OldRadioGuy2/Arduino-Controlled-Radio/Software/Arduino/src/commands.h

/*
Software Controlled Radio - Command Definitions
*/

#ifndef COMMANDS_H
#define COMMANDS_H

#define triggerPin      13       // pin to charge the capacitor - connected to one end of the charging resistor
#define pulseInPin      10
#define digitalBandSwitch    A1

#define analogVolumePin      0
#define analogBandSwitch     1

#define BLE_TxPin      11 
#define BLE_RxPin      12

#define RSP_BUF_SIZE 40

typedef const char * processor_t(char * cmd);
typedef processor_t * processor_p;

typedef struct {
    char cmd[4];
    processor_p processor;
} command;

const char * read_Cap(char * cmd);
processor_t set_freq;
processor_t set_band;
processor_t set_volume;

processor_t get_sig_lvl;
processor_t get_freq;
processor_t get_band;
processor_t get_volume;

processor_t volume_feature;
processor_t tuning_feature;
processor_t band_sw_feature;
processor_t display_feature;
processor_t save_cfg;
processor_t create_band;
processor_t delete_band;
processor_t calibrate_tuner;
processor_t calibrate_band;

// extern command command_list[];
// Error codes (commands always return * strings)
// #define SUCCESS "0"
// #define INVALID_COMMAND "-1"
// #define INVALID_ARG "-2"

extern char dbg_verbose;
extern char fmt_rsp_buffer[RSP_BUF_SIZE];

#endif
