OldRadioGuy2/Arduino-Controlled-Radio/Software/PC/src/gui/MainWindow.py

# -*- coding: utf-8 -*-

###########################################################################
## Python code generated with wxFormBuilder (version Oct 26 2018)
## http://www.wxformbuilder.org/
##
## PLEASE DO *NOT* EDIT THIS FILE!
###########################################################################

import wx
import wx.xrc

###########################################################################
## Class MainWindow
###########################################################################

class MainWindow ( wx.Frame ):

	def __init__( self, parent ):
		wx.Frame.__init__ ( self, parent, id = wx.ID_ANY, title = u"Arduino Radio", pos = wx.DefaultPosition, size = wx.Size( 729,700 ), style = wx.DEFAULT_FRAME_STYLE|wx.TAB_TRAVERSAL )

		self.SetSizeHints( wx.DefaultSize, wx.DefaultSize )

		self.m_menubar1 = wx.MenuBar( 0 )
		self.m_menu1 = wx.Menu()
		self.file_select_port = wx.MenuItem( self.m_menu1, wx.ID_ANY, u"Select Serial Port", wx.EmptyString, wx.ITEM_NORMAL )
		self.m_menu1.Append( self.file_select_port )

		self.file_load_config = wx.MenuItem( self.m_menu1, wx.ID_ANY, u"Load Configuration", wx.EmptyString, wx.ITEM_NORMAL )
		self.m_menu1.Append( self.file_load_config )

		self.file_save_config = wx.MenuItem( self.m_menu1, wx.ID_ANY, u"Save Configuration", wx.EmptyString, wx.ITEM_NORMAL )
		self.m_menu1.Append( self.file_save_config )

		self.file_exit = wx.MenuItem( self.m_menu1, wx.ID_ANY, u"Exit", wx.EmptyString, wx.ITEM_NORMAL )
		self.m_menu1.Append( self.file_exit )

		self.m_menubar1.Append( self.m_menu1, u"File" )

		self.m_menu4 = wx.Menu()
		self.configure_configure = wx.MenuItem( self.m_menu4, wx.ID_ANY, u"Configure", wx.EmptyString, wx.ITEM_NORMAL )
		self.m_menu4.Append( self.configure_configure )

		self.m_menubar1.Append( self.m_menu4, u"Configure" )

		self.m_menu2 = wx.Menu()
		self.m_menubar1.Append( self.m_menu2, u"Calibrate" )

		self.m_menu3 = wx.Menu()
		self.m_menubar1.Append( self.m_menu3, u"Help" )

		self.SetMenuBar( self.m_menubar1 )

		self.status_bar = self.CreateStatusBar( 4, 0, wx.ID_ANY )
		bSizer1 = wx.BoxSizer( wx.VERTICAL )

		self.m_staticText1 = wx.StaticText( self, wx.ID_ANY, u"Tuning", wx.DefaultPosition, wx.DefaultSize, 0 )
		self.m_staticText1.Wrap( -1 )

		bSizer1.Add( self.m_staticText1, 0, wx.ALL, 5 )

		bSizer2 = wx.BoxSizer( wx.HORIZONTAL )


		bSizer2.Add( ( 10, 0), 0, wx.EXPAND, 5 )

		self.static_min_frequency = wx.StaticText( self, wx.ID_ANY, u"540", wx.DefaultPosition, wx.DefaultSize, 0 )
		self.static_min_frequency.Wrap( -1 )

		bSizer2.Add( self.static_min_frequency, 0, wx.ALL, 5 )


		bSizer2.Add( ( 0, 0), 1, wx.EXPAND, 5 )

		self.static_current_frequency = wx.StaticText( self, wx.ID_ANY, u"1030", wx.DefaultPosition, wx.DefaultSize, 0 )
		self.static_current_frequency.Wrap( -1 )

		bSizer2.Add( self.static_current_frequency, 0, wx.ALL, 5 )


		bSizer2.Add( ( 0, 0), 1, wx.EXPAND, 5 )

		self.static_max_frequency = wx.StaticText( self, wx.ID_ANY, u"1620", wx.DefaultPosition, wx.DefaultSize, 0 )
		self.static_max_frequency.Wrap( -1 )

		bSizer2.Add( self.static_max_frequency, 0, wx.ALL, 5 )


		bSizer2.Add( ( 20, 0), 0, wx.EXPAND, 5 )


		bSizer1.Add( bSizer2, 0, wx.EXPAND, 5 )

		bSizer3 = wx.BoxSizer( wx.HORIZONTAL )

		self.tuning_slider=wx.Slider(self, size=wx.DefaultSize)
		bSizer3.Add( self.tuning_slider, 0, wx.ALL, 5 )


		bSizer1.Add( bSizer3, 0, wx.EXPAND, 5 )

		bSizer5 = wx.BoxSizer( wx.HORIZONTAL )


		bSizer5.Add( ( 150, 0), 0, wx.EXPAND, 5 )

		self.scan_down_button = wx.BitmapButton( self, wx.ID_ANY, wx.NullBitmap, wx.DefaultPosition, wx.DefaultSize, wx.BU_AUTODRAW|0 )

		self.scan_down_button.SetBitmap( wx.ArtProvider.GetBitmap( wx.ART_GO_BACK,  ) )
		bSizer5.Add( self.scan_down_button, 0, wx.ALL, 5 )


		bSizer5.Add( ( 50, 0), 1, wx.EXPAND, 5 )

		self.scan_up_button = wx.BitmapButton( self, wx.ID_ANY, wx.NullBitmap, wx.DefaultPosition, wx.DefaultSize, wx.BU_AUTODRAW|0 )

		self.scan_up_button.SetBitmap( wx.ArtProvider.GetBitmap( wx.ART_GO_FORWARD,  ) )
		bSizer5.Add( self.scan_up_button, 0, wx.ALL, 5 )


		bSizer5.Add( ( 150, 0), 0, wx.EXPAND, 5 )


		bSizer1.Add( bSizer5, 0, wx.EXPAND, 5 )

		self.m_staticline1 = wx.StaticLine( self, wx.ID_ANY, wx.DefaultPosition, wx.DefaultSize, wx.LI_HORIZONTAL )
		bSizer1.Add( self.m_staticline1, 0, wx.EXPAND |wx.ALL, 5 )

		bSizer4 = wx.BoxSizer( wx.HORIZONTAL )


		bSizer4.Add( ( 40, 0), 0, wx.EXPAND, 5 )

		self.m_staticText5 = wx.StaticText( self, wx.ID_ANY, u"Volume", wx.DefaultPosition, wx.DefaultSize, 0 )
		self.m_staticText5.Wrap( -1 )

		bSizer4.Add( self.m_staticText5, 0, wx.ALIGN_CENTER_VERTICAL|wx.ALL, 5 )

		self.volume_control = wx.SpinCtrl( self, wx.ID_ANY, wx.EmptyString, wx.DefaultPosition, wx.DefaultSize, wx.SP_ARROW_KEYS, 0, 64, 33 )
		bSizer4.Add( self.volume_control, 0, wx.ALL, 5 )


		bSizer4.Add( ( 0, 0), 1, wx.EXPAND, 5 )

		self.m_staticText6 = wx.StaticText( self, wx.ID_ANY, u"Band", wx.DefaultPosition, wx.DefaultSize, 0 )
		self.m_staticText6.Wrap( -1 )

		bSizer4.Add( self.m_staticText6, 0, wx.ALIGN_CENTER_VERTICAL|wx.ALL, 5 )

		band_switchChoices = [ u"AM:  540-1620kHz", u"SW1: 1.7-4.0MHz", u"80M Ham: 3.5-4.0MHz", u"FM: 88-108MHz", wx.EmptyString ]
		self.band_switch = wx.Choice( self, wx.ID_ANY, wx.DefaultPosition, wx.DefaultSize, band_switchChoices, 0 )
		self.band_switch.SetSelection( 0 )
		self.band_switch.SetMinSize( wx.Size( 300,-1 ) )

		bSizer4.Add( self.band_switch, 0, wx.ALL, 5 )


		bSizer4.Add( ( 0, 0), 1, wx.EXPAND, 5 )


		bSizer1.Add( bSizer4, 0, wx.EXPAND, 5 )

		self.m_staticline2 = wx.StaticLine( self, wx.ID_ANY, wx.DefaultPosition, wx.DefaultSize, wx.LI_HORIZONTAL )
		bSizer1.Add( self.m_staticline2, 0, wx.EXPAND |wx.ALL, 5 )

		bSizer6 = wx.BoxSizer( wx.HORIZONTAL )


		bSizer6.Add( ( 20, 0), 0, wx.EXPAND, 5 )

		self.m_staticText7 = wx.StaticText( self, wx.ID_ANY, u"Signal Level", wx.DefaultPosition, wx.DefaultSize, 0 )
		self.m_staticText7.Wrap( -1 )

		bSizer6.Add( self.m_staticText7, 0, wx.ALIGN_TOP|wx.ALL, 5 )

		self.signal_level_guage = wx.Gauge( self, wx.ID_ANY, 255, wx.DefaultPosition, wx.DefaultSize, wx.GA_HORIZONTAL|wx.GA_SMOOTH )
		self.signal_level_guage.SetValue( 128 )
		bSizer6.Add( self.signal_level_guage, 0, wx.ALL, 5 )


		bSizer6.Add( ( 0, 0), 1, wx.EXPAND, 5 )

		self.m_staticText8 = wx.StaticText( self, wx.ID_ANY, u"S/N Ratio", wx.DefaultPosition, wx.DefaultSize, 0 )
		self.m_staticText8.Wrap( -1 )

		bSizer6.Add( self.m_staticText8, 0, wx.ALIGN_CENTER_VERTICAL|wx.ALL, 5 )

		self.m_gauge2 = wx.Gauge( self, wx.ID_ANY, 256, wx.DefaultPosition, wx.DefaultSize, wx.GA_HORIZONTAL|wx.GA_SMOOTH )
		self.m_gauge2.SetValue( 128 )
		bSizer6.Add( self.m_gauge2, 0, wx.ALIGN_TOP|wx.ALL, 5 )


		bSizer6.Add( ( 20, 0), 1, wx.EXPAND, 5 )


		bSizer1.Add( bSizer6, 0, wx.EXPAND, 5 )

		bSizer7 = wx.BoxSizer( wx.VERTICAL )

		self.terminal_text_ctrl = wx.TextCtrl( self, wx.ID_ANY, wx.EmptyString, wx.DefaultPosition, wx.DefaultSize, wx.TE_MULTILINE|wx.TE_READONLY )
		bSizer7.Add( self.terminal_text_ctrl, 1, wx.ALL|wx.EXPAND, 5 )

		self.m_staticText9 = wx.StaticText( self, wx.ID_ANY, u"Enter Command", wx.DefaultPosition, wx.DefaultSize, 0 )
		self.m_staticText9.Wrap( -1 )

		bSizer7.Add( self.m_staticText9, 0, wx.ALL, 5 )

		self.command_entry = wx.TextCtrl( self, wx.ID_ANY, wx.EmptyString, wx.DefaultPosition, wx.Size( -1,-1 ), wx.TE_PROCESS_ENTER )
		self.command_entry.SetMinSize( wx.Size( -1,30 ) )

		bSizer7.Add( self.command_entry, 0, wx.ALL|wx.EXPAND, 5 )


		bSizer1.Add( bSizer7, 1, wx.EXPAND, 5 )


		self.SetSizer( bSizer1 )
		self.Layout()

		self.Centre( wx.BOTH )

		# Connect Events
		self.Bind( wx.EVT_CLOSE, self.MainWindowOnClose )
		self.Bind( wx.EVT_SHOW, self.MainWindowOnShow )
		self.Bind( wx.EVT_SIZE, self.MainWindowOnSize )
		self.Bind( wx.EVT_MENU, self.file_select_portOnMenuSelection, id = self.file_select_port.GetId() )
		self.Bind( wx.EVT_MENU, self.file_exitOnMenuSelection, id = self.file_exit.GetId() )
		self.Bind( wx.EVT_MENU, self.configure_configureOnMenuSelection, id = self.configure_configure.GetId() )
		self.volume_control.Bind( wx.EVT_SPINCTRL, self.volume_controlOnSpinCtrl )
		self.band_switch.Bind( wx.EVT_CHOICE, self.band_switchOnChoice )
		self.command_entry.Bind( wx.EVT_TEXT_ENTER, self.command_entryOnTextEnter )

	def __del__( self ):
		pass


	# Virtual event handlers, overide them in your derived class
	def MainWindowOnClose( self, event ):
		event.Skip()

	def MainWindowOnShow( self, event ):
		event.Skip()

	def MainWindowOnSize( self, event ):
		event.Skip()

	def file_select_portOnMenuSelection( self, event ):
		event.Skip()

	def file_exitOnMenuSelection( self, event ):
		event.Skip()

	def configure_configureOnMenuSelection( self, event ):
		event.Skip()

	def volume_controlOnSpinCtrl( self, event ):
		event.Skip()

	def band_switchOnChoice( self, event ):
		event.Skip()

	def command_entryOnTextEnter( self, event ):
		event.Skip()


###########################################################################
## Class SelectPortDlg
###########################################################################

class SelectPortDlg ( wx.Dialog ):

	def __init__( self, parent ):
		wx.Dialog.__init__ ( self, parent, id = wx.ID_ANY, title = u"Select Serial Port", pos = wx.DefaultPosition, size = wx.Size( 336,261 ), style = wx.DEFAULT_DIALOG_STYLE )

		self.SetSizeHints( wx.DefaultSize, wx.DefaultSize )

		bSizer8 = wx.BoxSizer( wx.VERTICAL )


		bSizer8.Add( ( 0, 40), 0, wx.EXPAND, 5 )

		bSizer9 = wx.BoxSizer( wx.HORIZONTAL )

		gSizer1 = wx.GridSizer( 2, 2, 0, 0 )

		self.m_staticText10 = wx.StaticText( self, wx.ID_ANY, u"Port:", wx.DefaultPosition, wx.DefaultSize, 0 )
		self.m_staticText10.Wrap( -1 )

		gSizer1.Add( self.m_staticText10, 0, wx.LEFT, 5 )

		self.m_staticText11 = wx.StaticText( self, wx.ID_ANY, u"Baud Rate:", wx.DefaultPosition, wx.DefaultSize, 0 )
		self.m_staticText11.Wrap( -1 )

		gSizer1.Add( self.m_staticText11, 0, wx.LEFT, 5 )

		port_chooserChoices = []
		self.port_chooser = wx.Choice( self, wx.ID_ANY, wx.DefaultPosition, wx.DefaultSize, port_chooserChoices, 0 )
		self.port_chooser.SetSelection( 0 )
		gSizer1.Add( self.port_chooser, 0, wx.LEFT, 5 )

		baud_rate_chooserChoices = [ u"1200", u"9600", u"19200", u"115200", wx.EmptyString, wx.EmptyString ]
		self.baud_rate_chooser = wx.Choice( self, wx.ID_ANY, wx.DefaultPosition, wx.DefaultSize, baud_rate_chooserChoices, 0 )
		self.baud_rate_chooser.SetSelection( 1 )
		gSizer1.Add( self.baud_rate_chooser, 0, wx.LEFT, 5 )


		bSizer9.Add( gSizer1, 1, wx.EXPAND, 5 )


		bSizer8.Add( bSizer9, 0, wx.EXPAND, 5 )


		bSizer8.Add( ( 0, 0), 1, wx.EXPAND, 5 )

		m_sdbSizer1 = wx.StdDialogButtonSizer()
		self.m_sdbSizer1OK = wx.Button( self, wx.ID_OK )
		m_sdbSizer1.AddButton( self.m_sdbSizer1OK )
		self.m_sdbSizer1Cancel = wx.Button( self, wx.ID_CANCEL )
		m_sdbSizer1.AddButton( self.m_sdbSizer1Cancel )
		m_sdbSizer1.Realize();

		bSizer8.Add( m_sdbSizer1, 0, wx.BOTTOM|wx.EXPAND, 5 )


		self.SetSizer( bSizer8 )
		self.Layout()

		self.Centre( wx.BOTH )

		# Connect Events
		self.Bind( wx.EVT_INIT_DIALOG, self.SelectPortDlgOnInitDialog )
		self.port_chooser.Bind( wx.EVT_CHOICE, self.port_chooserOnChoice )
		self.m_sdbSizer1Cancel.Bind( wx.EVT_BUTTON, self.on_cancel_button_click )
		self.m_sdbSizer1OK.Bind( wx.EVT_BUTTON, self.on_ok_button_click )

	def __del__( self ):
		pass


	# Virtual event handlers, overide them in your derived class
	def SelectPortDlgOnInitDialog( self, event ):
		event.Skip()

	def port_chooserOnChoice( self, event ):
		event.Skip()

	def on_cancel_button_click( self, event ):
		event.Skip()

	def on_ok_button_click( self, event ):
		event.Skip()


###########################################################################
## Class ConfigurationDlg
###########################################################################

class ConfigurationDlg ( wx.Dialog ):

	def __init__( self, parent ):
		wx.Dialog.__init__ ( self, parent, id = wx.ID_ANY, title = u"Configuration", pos = wx.DefaultPosition, size = wx.Size( 591,442 ), style = wx.DEFAULT_DIALOG_STYLE|wx.RESIZE_BORDER )

		self.SetSizeHints( wx.DefaultSize, wx.DefaultSize )

		bSizer11 = wx.BoxSizer( wx.VERTICAL )

		self.configuration_page = wx.Notebook( self, wx.ID_ANY, wx.DefaultPosition, wx.DefaultSize, 0 )
		self.m_panel1 = wx.Panel( self.configuration_page, wx.ID_ANY, wx.DefaultPosition, wx.DefaultSize, wx.TAB_TRAVERSAL )
		bSizer12 = wx.BoxSizer( wx.VERTICAL )

		bSizer21 = wx.BoxSizer( wx.HORIZONTAL )

		gSizer2 = wx.GridSizer( 3, 2, 0, 0 )

		self.enable_tuning_cb = wx.CheckBox( self.m_panel1, wx.ID_ANY, u"Enable Tuning Control", wx.DefaultPosition, wx.DefaultSize, 0 )
		gSizer2.Add( self.enable_tuning_cb, 0, wx.ALIGN_CENTER_VERTICAL|wx.ALL, 5 )

		self.calibrate_tuning_btn = wx.Button( self.m_panel1, wx.ID_ANY, u"Calibrate", wx.DefaultPosition, wx.DefaultSize, 0 )
		gSizer2.Add( self.calibrate_tuning_btn, 0, wx.ALL, 5 )

		self.enable_volume_cb = wx.CheckBox( self.m_panel1, wx.ID_ANY, u"Enable Volume Control", wx.DefaultPosition, wx.DefaultSize, 0 )
		gSizer2.Add( self.enable_volume_cb, 0, wx.ALIGN_CENTER_VERTICAL|wx.ALL, 5 )

		self.calibrate_volume_btn = wx.Button( self.m_panel1, wx.ID_ANY, u"Calibrate", wx.DefaultPosition, wx.DefaultSize, 0 )
		gSizer2.Add( self.calibrate_volume_btn, 0, wx.ALL, 5 )

		self.enable_band_switch_cb = wx.CheckBox( self.m_panel1, wx.ID_ANY, u"Enable Band Switch", wx.DefaultPosition, wx.DefaultSize, 0 )
		gSizer2.Add( self.enable_band_switch_cb, 0, wx.ALIGN_CENTER_VERTICAL|wx.ALL, 5 )

		self.calibrate_tuning_btn2 = wx.Button( self.m_panel1, wx.ID_ANY, u"Calibrate", wx.DefaultPosition, wx.DefaultSize, 0 )
		gSizer2.Add( self.calibrate_tuning_btn2, 0, wx.ALL, 5 )


		bSizer21.Add( gSizer2, 0, wx.EXPAND, 5 )


		bSizer12.Add( bSizer21, 0, wx.EXPAND, 5 )


		self.m_panel1.SetSizer( bSizer12 )
		self.m_panel1.Layout()
		bSizer12.Fit( self.m_panel1 )
		self.configuration_page.AddPage( self.m_panel1, u"General", False )
		self.band_panel = wx.Panel( self.configuration_page, wx.ID_ANY, wx.DefaultPosition, wx.DefaultSize, wx.TAB_TRAVERSAL )
		bSizer22 = wx.BoxSizer( wx.VERTICAL )

		bSizer23 = wx.BoxSizer( wx.HORIZONTAL )

		self.band_list_ctrl = wx.ListCtrl( self.band_panel, wx.ID_ANY, wx.DefaultPosition, wx.DefaultSize, wx.LC_REPORT|wx.LC_SINGLE_SEL )
		self.band_list_ctrl.SetMinSize( wx.Size( 500,-1 ) )

		bSizer23.Add( self.band_list_ctrl, 0, wx.ALL|wx.EXPAND, 5 )

		bSizer24 = wx.BoxSizer( wx.VERTICAL )

		self.add_band_btn = wx.BitmapButton( self.band_panel, wx.ID_ANY, wx.NullBitmap, wx.DefaultPosition, wx.DefaultSize, wx.BU_AUTODRAW|0 )

		self.add_band_btn.SetBitmap( wx.ArtProvider.GetBitmap( wx.ART_NEW,  ) )
		bSizer24.Add( self.add_band_btn, 0, wx.ALIGN_RIGHT|wx.ALL|wx.RIGHT, 5 )

		self.remove_band_btn = wx.BitmapButton( self.band_panel, wx.ID_ANY, wx.NullBitmap, wx.DefaultPosition, wx.DefaultSize, wx.BU_AUTODRAW|0 )

		self.remove_band_btn.SetBitmap( wx.ArtProvider.GetBitmap( wx.ART_DELETE,  ) )
		bSizer24.Add( self.remove_band_btn, 0, wx.ALIGN_RIGHT|wx.ALL, 5 )

		self.move_band_up_btn = wx.BitmapButton( self.band_panel, wx.ID_ANY, wx.NullBitmap, wx.DefaultPosition, wx.DefaultSize, wx.BU_AUTODRAW|0 )

		self.move_band_up_btn.SetBitmap( wx.ArtProvider.GetBitmap( wx.ART_GO_UP,  ) )
		bSizer24.Add( self.move_band_up_btn, 0, wx.ALIGN_RIGHT|wx.ALL, 5 )

		self.move_band_down_btn = wx.BitmapButton( self.band_panel, wx.ID_ANY, wx.NullBitmap, wx.DefaultPosition, wx.DefaultSize, wx.BU_AUTODRAW|0 )

		self.move_band_down_btn.SetBitmap( wx.ArtProvider.GetBitmap( wx.ART_GO_DOWN,  ) )
		bSizer24.Add( self.move_band_down_btn, 0, wx.ALIGN_RIGHT|wx.ALL, 5 )


		bSizer23.Add( bSizer24, 1, wx.EXPAND, 5 )


		bSizer22.Add( bSizer23, 1, wx.EXPAND, 5 )


		self.band_panel.SetSizer( bSizer22 )
		self.band_panel.Layout()
		bSizer22.Fit( self.band_panel )
		self.configuration_page.AddPage( self.band_panel, u"Bands", True )

		bSizer11.Add( self.configuration_page, 1, wx.EXPAND |wx.ALL, 5 )

		bSizer13 = wx.BoxSizer( wx.HORIZONTAL )


		bSizer13.Add( ( 0, 0), 1, wx.EXPAND, 5 )

		self.ok_btn = wx.Button( self, wx.ID_ANY, u"OK", wx.DefaultPosition, wx.DefaultSize, 0 )
		bSizer13.Add( self.ok_btn, 0, wx.ALL, 5 )

		self.cancel_btn = wx.Button( self, wx.ID_ANY, u"Cancel", wx.DefaultPosition, wx.DefaultSize, 0 )
		bSizer13.Add( self.cancel_btn, 0, wx.ALL, 5 )


		bSizer11.Add( bSizer13, 0, wx.EXPAND, 5 )


		self.SetSizer( bSizer11 )
		self.Layout()

		self.Centre( wx.BOTH )

		# Connect Events
		self.Bind( wx.EVT_INIT_DIALOG, self.ConfigurationDlgOnInitDialog )
		self.configuration_page.Bind( wx.EVT_NOTEBOOK_PAGE_CHANGED, self.configuration_pageOnNotebookPageChanged )
		self.band_list_ctrl.Bind( wx.EVT_LIST_ITEM_ACTIVATED, self.band_list_ctrlOnListItemActivated )
		self.band_list_ctrl.Bind( wx.EVT_LIST_ITEM_SELECTED, self.band_list_ctrlOnListItemSelected )
		self.add_band_btn.Bind( wx.EVT_BUTTON, self.add_band_btnOnButtonClick )
		self.remove_band_btn.Bind( wx.EVT_BUTTON, self.remove_band_btnOnButtonClick )
		self.move_band_up_btn.Bind( wx.EVT_BUTTON, self.move_band_up_btnOnButtonClick )
		self.move_band_down_btn.Bind( wx.EVT_BUTTON, self.move_band_down_btnOnButtonClick )
		self.ok_btn.Bind( wx.EVT_BUTTON, self.ok_btnOnButtonClick )
		self.cancel_btn.Bind( wx.EVT_BUTTON, self.cancel_btnOnButtonClick )

	def __del__( self ):
		pass


	# Virtual event handlers, overide them in your derived class
	def ConfigurationDlgOnInitDialog( self, event ):
		event.Skip()

	def configuration_pageOnNotebookPageChanged( self, event ):
		event.Skip()

	def band_list_ctrlOnListItemActivated( self, event ):
		event.Skip()

	def band_list_ctrlOnListItemSelected( self, event ):
		event.Skip()

	def add_band_btnOnButtonClick( self, event ):
		event.Skip()

	def remove_band_btnOnButtonClick( self, event ):
		event.Skip()

	def move_band_up_btnOnButtonClick( self, event ):
		event.Skip()

	def move_band_down_btnOnButtonClick( self, event ):
		event.Skip()

	def ok_btnOnButtonClick( self, event ):
		event.Skip()

	def cancel_btnOnButtonClick( self, event ):
		event.Skip()


###########################################################################
## Class EditBandDlg
###########################################################################

class EditBandDlg ( wx.Dialog ):

	def __init__( self, parent ):
		wx.Dialog.__init__ ( self, parent, id = wx.ID_ANY, title = u"Edit Band Information", pos = wx.DefaultPosition, size = wx.Size( 355,286 ), style = wx.DEFAULT_DIALOG_STYLE|wx.RESIZE_BORDER )

		self.SetSizeHints( wx.Size( -1,-1 ), wx.DefaultSize )

		bSizer26 = wx.BoxSizer( wx.VERTICAL )

		gSizer3 = wx.GridSizer( 0, 2, 0, 0 )

		self.m_staticText12 = wx.StaticText( self, wx.ID_ANY, u"Label:", wx.DefaultPosition, wx.DefaultSize, 0 )
		self.m_staticText12.Wrap( -1 )

		gSizer3.Add( self.m_staticText12, 0, wx.ALIGN_CENTER_VERTICAL|wx.ALIGN_RIGHT|wx.ALL, 5 )

		self.band_label_txt = wx.TextCtrl( self, wx.ID_ANY, wx.EmptyString, wx.DefaultPosition, wx.DefaultSize, 0 )
		self.band_label_txt.SetMinSize( wx.Size( 150,-1 ) )

		gSizer3.Add( self.band_label_txt, 0, wx.ALL, 5 )

		self.m_staticText13 = wx.StaticText( self, wx.ID_ANY, u"Min. Freq.:", wx.DefaultPosition, wx.DefaultSize, 0 )
		self.m_staticText13.Wrap( -1 )

		gSizer3.Add( self.m_staticText13, 0, wx.ALIGN_CENTER_VERTICAL|wx.ALIGN_RIGHT|wx.ALL, 5 )

		self.min_freq_dbl_spin = wx.SpinCtrlDouble( self, wx.ID_ANY, wx.EmptyString, wx.DefaultPosition, wx.DefaultSize, wx.SP_ARROW_KEYS, 0, 100, 0, 0.01 )
		self.min_freq_dbl_spin.SetDigits( 2 )
		gSizer3.Add( self.min_freq_dbl_spin, 0, wx.ALL, 5 )

		self.m_staticText14 = wx.StaticText( self, wx.ID_ANY, u"Max. Freq.:", wx.DefaultPosition, wx.DefaultSize, 0 )
		self.m_staticText14.Wrap( -1 )

		gSizer3.Add( self.m_staticText14, 0, wx.ALIGN_CENTER_VERTICAL|wx.ALIGN_RIGHT|wx.ALL, 5 )

		self.max_freq_dbl_spin = wx.SpinCtrlDouble( self, wx.ID_ANY, wx.EmptyString, wx.DefaultPosition, wx.DefaultSize, wx.SP_ARROW_KEYS, 0, 100, 0, 0.01 )
		self.max_freq_dbl_spin.SetDigits( 2 )
		gSizer3.Add( self.max_freq_dbl_spin, 0, wx.ALL, 5 )

		self.m_staticText15 = wx.StaticText( self, wx.ID_ANY, u"Units:", wx.DefaultPosition, wx.DefaultSize, 0 )
		self.m_staticText15.Wrap( -1 )

		gSizer3.Add( self.m_staticText15, 0, wx.ALIGN_CENTER_VERTICAL|wx.ALIGN_RIGHT|wx.ALL, 5 )

		units_choiceChoices = [ u"KHz", u"MHz" ]
		self.units_choice = wx.Choice( self, wx.ID_ANY, wx.DefaultPosition, wx.DefaultSize, units_choiceChoices, 0 )
		self.units_choice.SetSelection( 0 )
		gSizer3.Add( self.units_choice, 0, wx.ALL, 5 )

		self.m_staticText16 = wx.StaticText( self, wx.ID_ANY, u"Mode:", wx.DefaultPosition, wx.DefaultSize, 0 )
		self.m_staticText16.Wrap( -1 )

		gSizer3.Add( self.m_staticText16, 0, wx.ALIGN_CENTER_VERTICAL|wx.ALIGN_RIGHT|wx.ALL, 5 )

		mode_choiceChoices = [ u"AM", u"FM", u"SSB" ]
		self.mode_choice = wx.Choice( self, wx.ID_ANY, wx.DefaultPosition, wx.DefaultSize, mode_choiceChoices, 0 )
		self.mode_choice.SetSelection( 0 )
		gSizer3.Add( self.mode_choice, 0, wx.ALL, 5 )


		bSizer26.Add( gSizer3, 1, wx.EXPAND, 5 )

		bSizer27 = wx.BoxSizer( wx.HORIZONTAL )


		bSizer27.Add( ( 0, 0), 1, wx.EXPAND, 5 )

		self.ok_btn = wx.Button( self, wx.ID_ANY, u"OK", wx.DefaultPosition, wx.DefaultSize, 0 )
		bSizer27.Add( self.ok_btn, 0, wx.ALL, 5 )

		self.cancel_btn = wx.Button( self, wx.ID_ANY, u"Cancel", wx.DefaultPosition, wx.DefaultSize, 0 )
		bSizer27.Add( self.cancel_btn, 0, wx.ALL, 5 )


		bSizer26.Add( bSizer27, 0, wx.EXPAND, 5 )


		self.SetSizer( bSizer26 )
		self.Layout()

		self.Centre( wx.BOTH )

		# Connect Events
		self.Bind( wx.EVT_INIT_DIALOG, self.EditBandDlgOnInitDialog )
		self.ok_btn.Bind( wx.EVT_BUTTON, self.ok_btnOnButtonClick )
		self.cancel_btn.Bind( wx.EVT_BUTTON, self.cancel_btnOnButtonClick )

	def __del__( self ):
		pass


	# Virtual event handlers, overide them in your derived class
	def EditBandDlgOnInitDialog( self, event ):
		event.Skip()

	def ok_btnOnButtonClick( self, event ):
		event.Skip()

	def cancel_btnOnButtonClick( self, event ):
		event.Skip()
